qurihara/chordika/assets/cheatsheet_ja.png

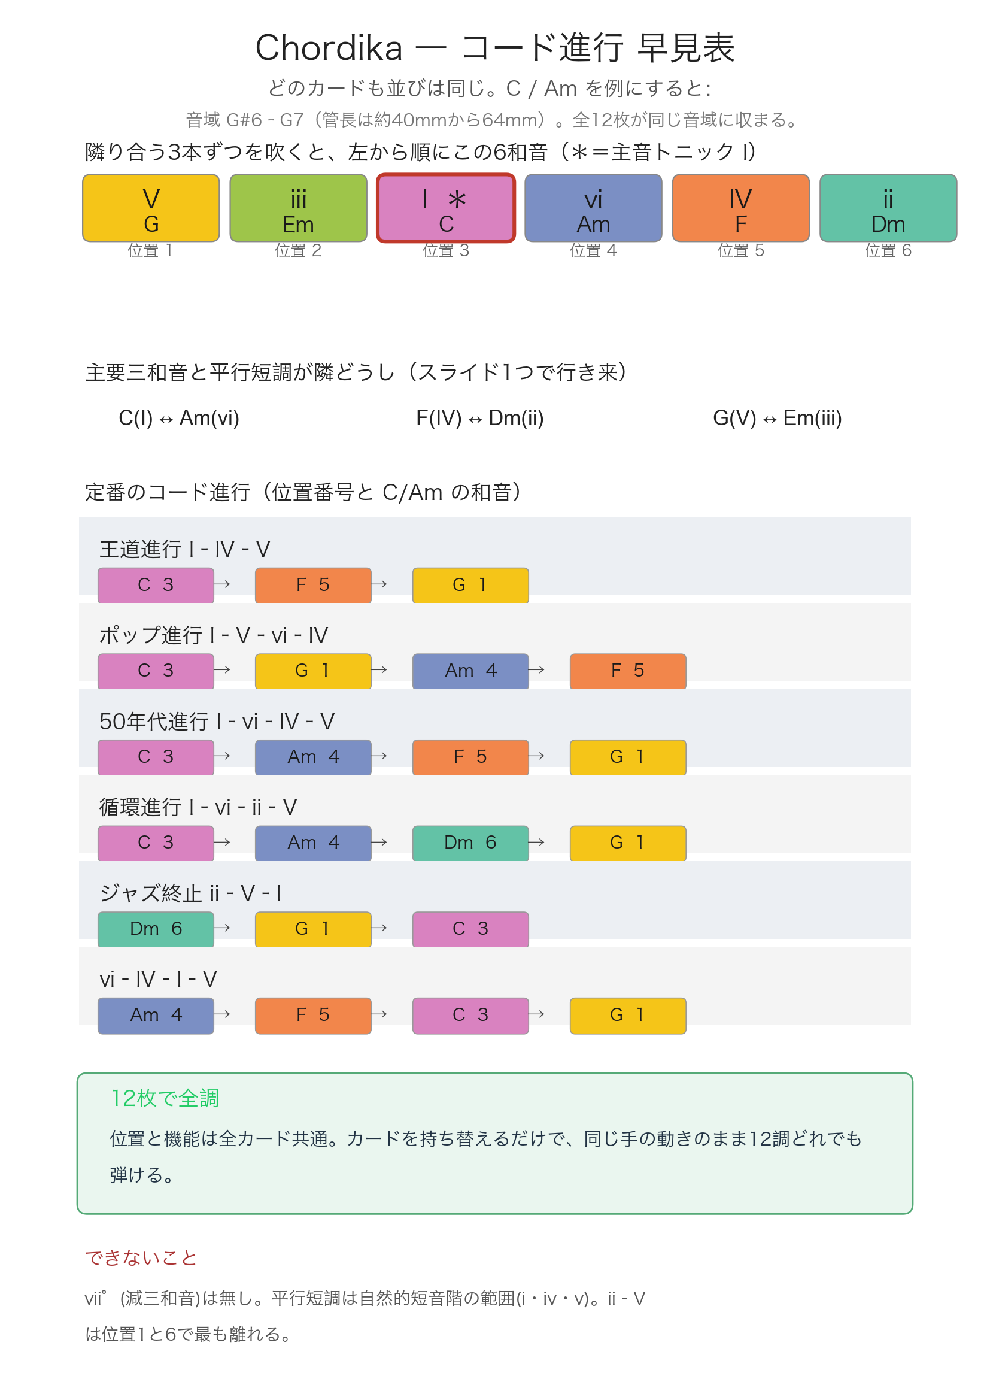
assets/cheatsheet_ja.png
