qurihara/chordika/assets/chord_map_A_Fsm.png

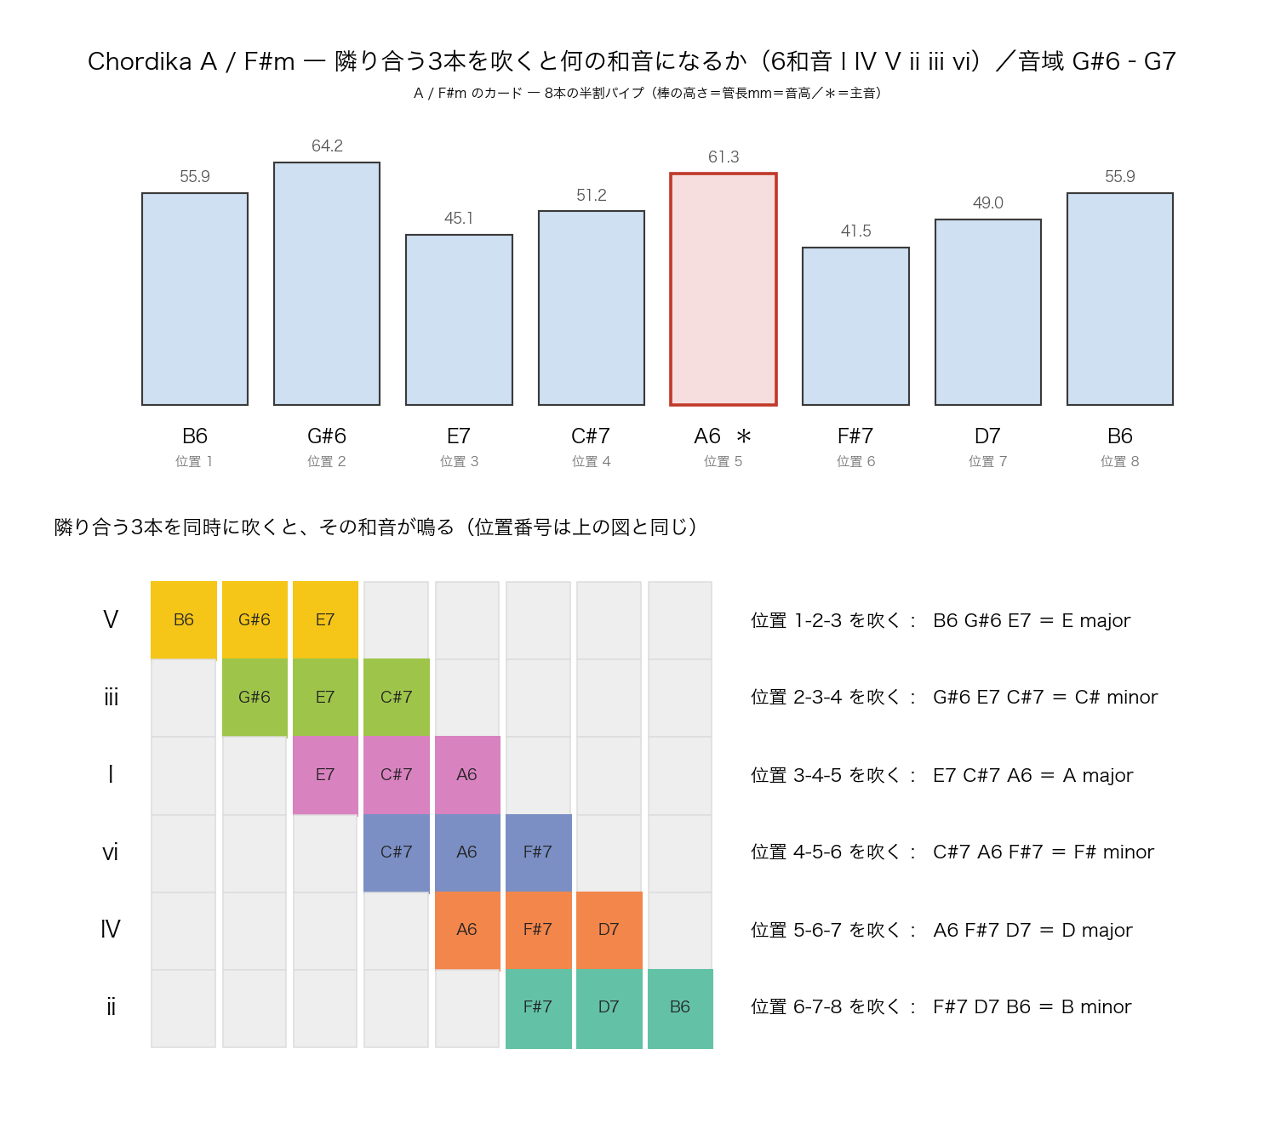
assets/chord_map_A_Fsm.png
