qurihara/chordika/assets/chord_map_Ab_Fm.png

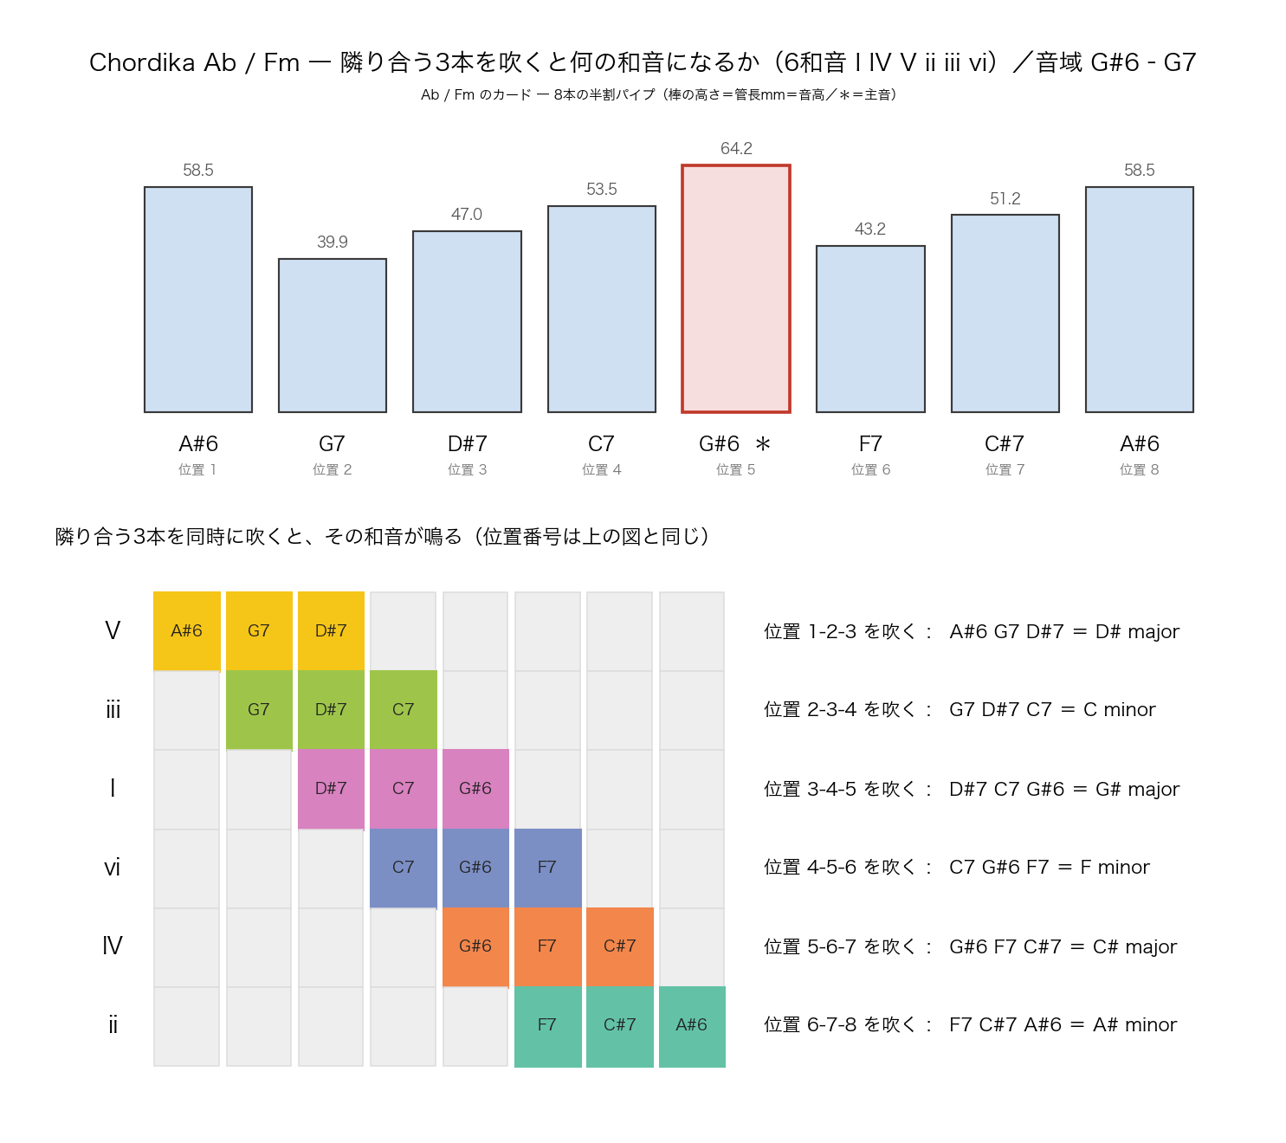
assets/chord_map_Ab_Fm.png
