qurihara/chordika/assets/chord_map_B_Gsm.png

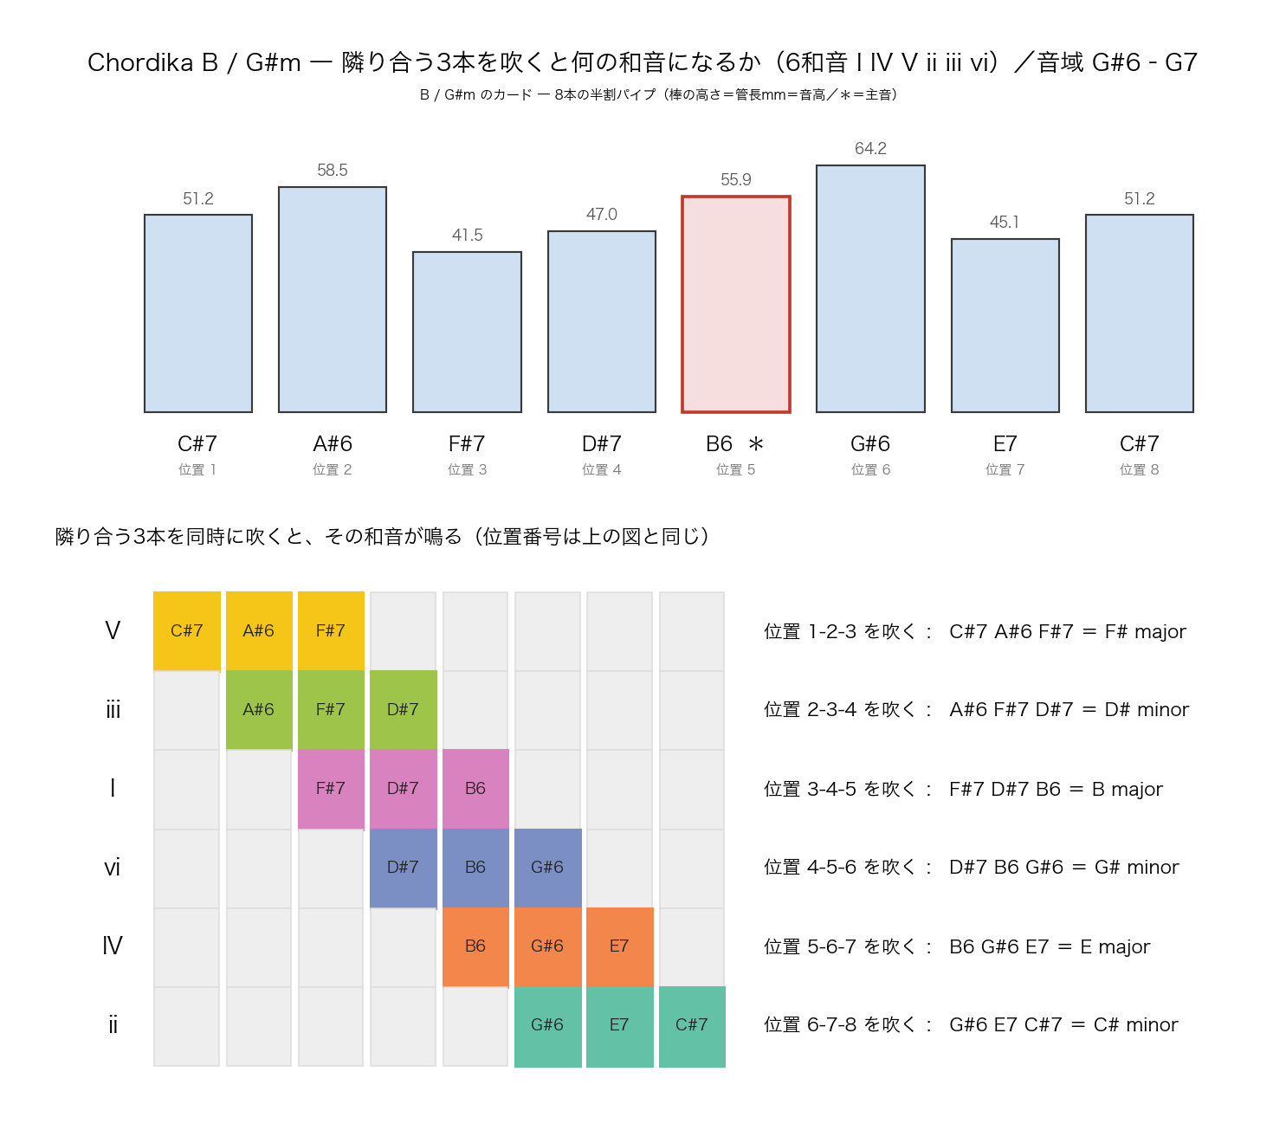
assets/chord_map_B_Gsm.png
