qurihara/chordika/assets/chord_map_D_Bm.png

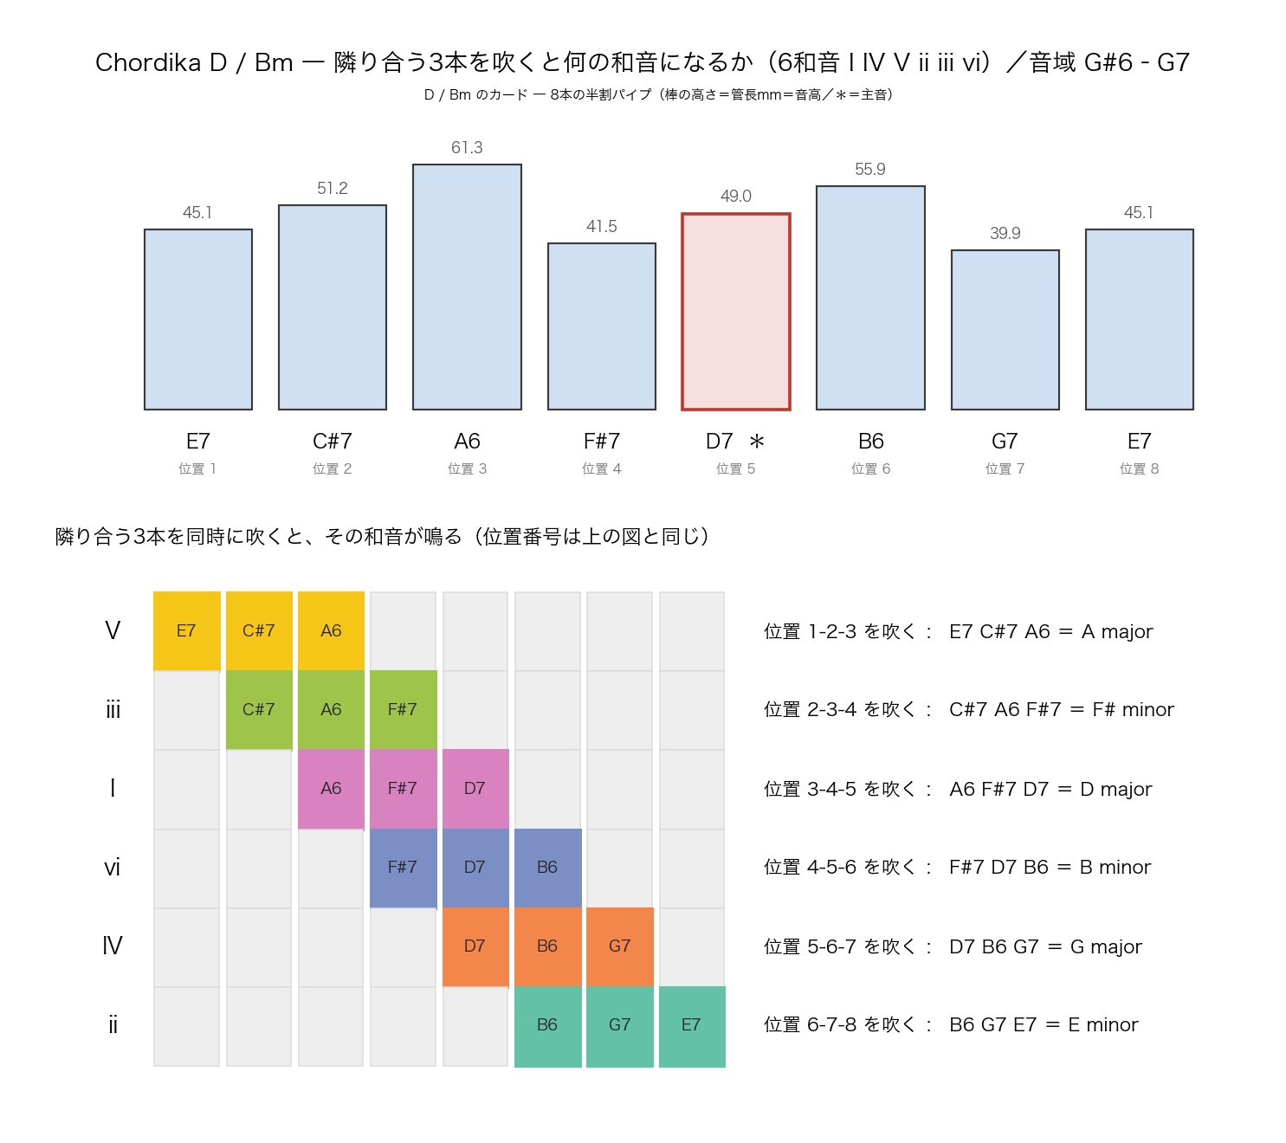
assets/chord_map_D_Bm.png
