qurihara/chordika/assets/chord_map_Db_Bbm.png

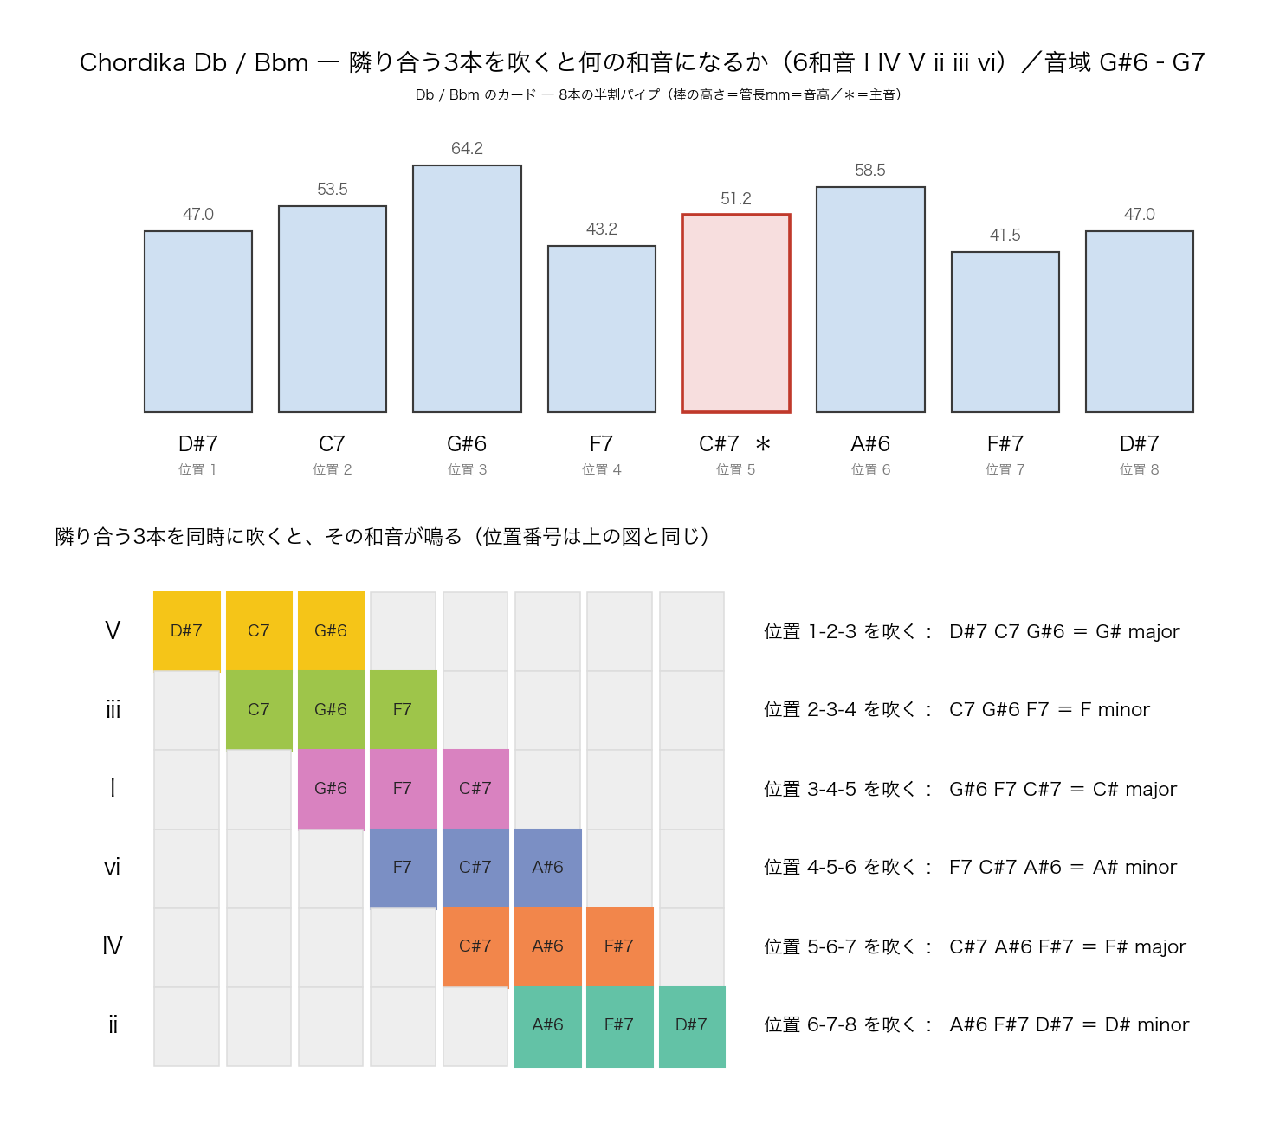
assets/chord_map_Db_Bbm.png
