qurihara/chordika/assets/chord_map_E_Csm.png

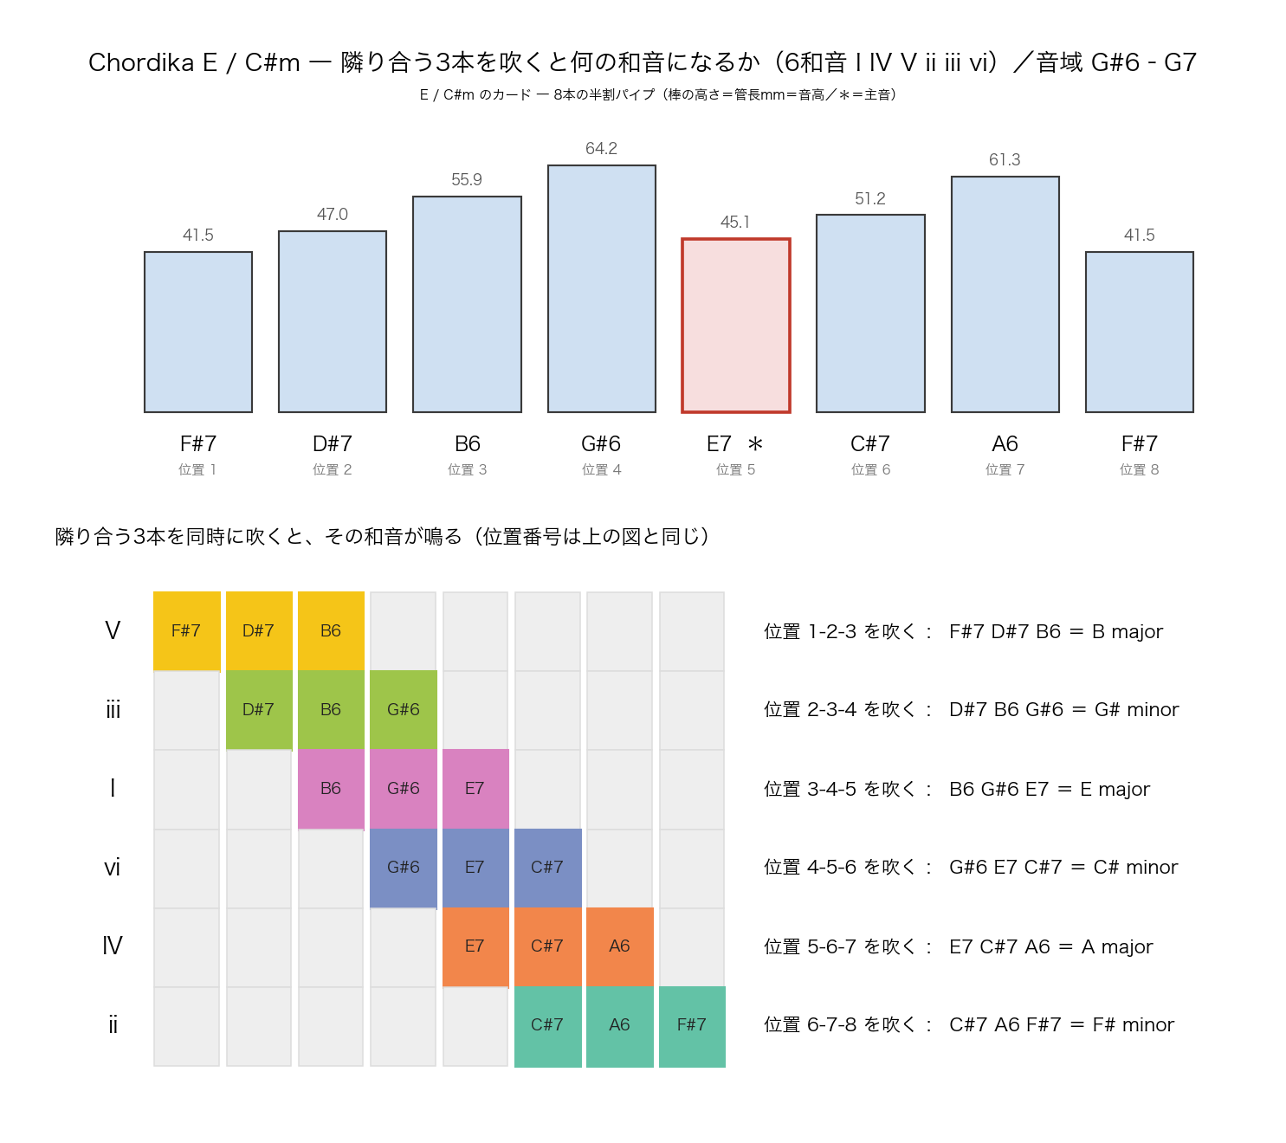
assets/chord_map_E_Csm.png
