qurihara/chordika/assets/photo_recorika.jpg

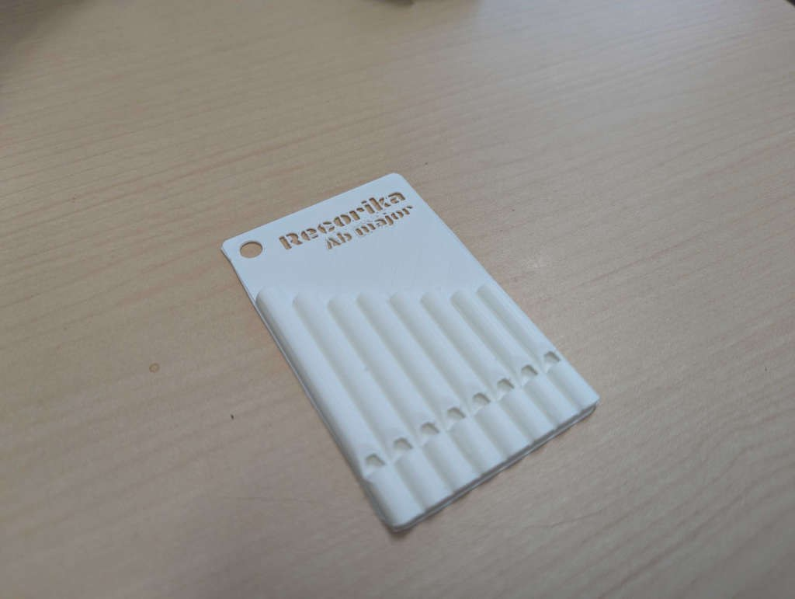
assets/photo_recorika.jpg
